vetal-esher/MT32-DIT/images/dit.png

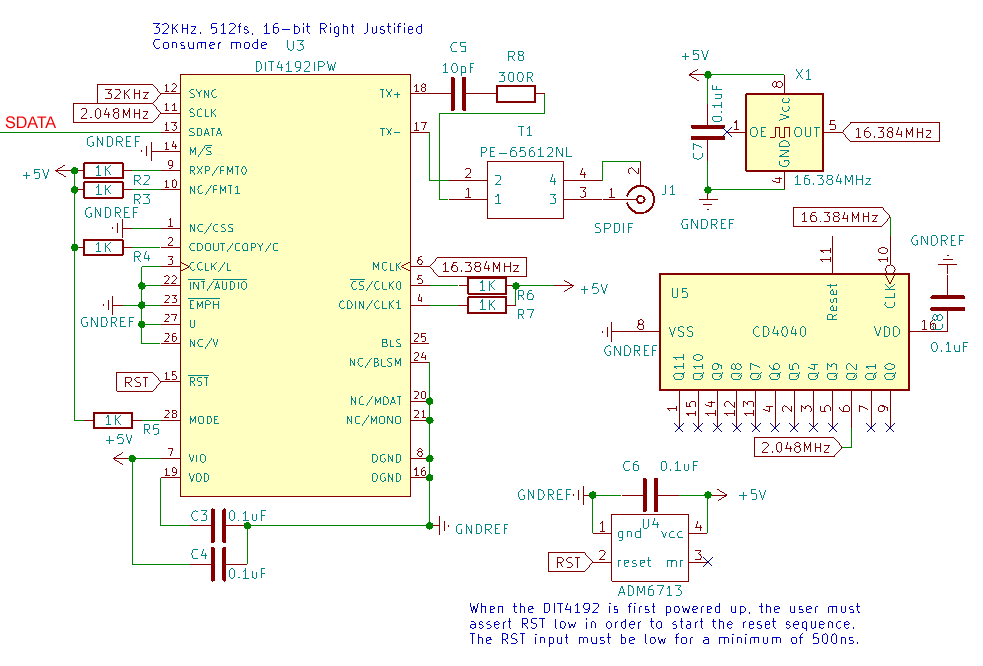
images/dit.png
