vetal-esher/MT32-DIT/images/oscil/A-B/pic_45_13.bmp

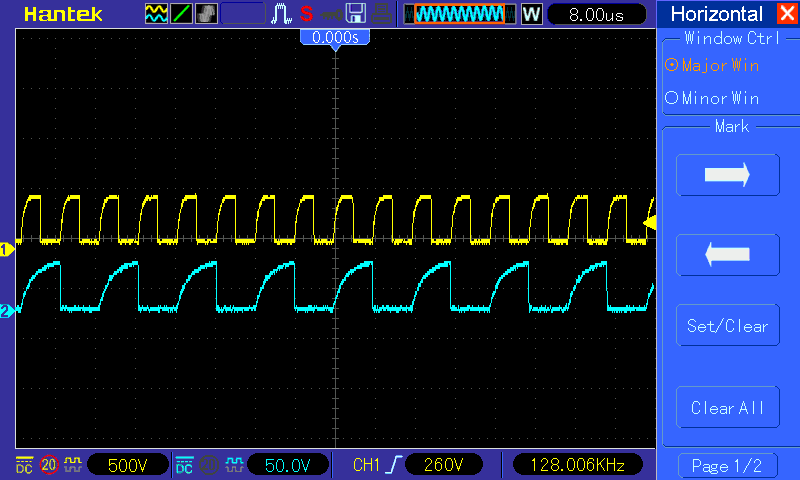
images/oscil/A-B/pic_45_13.bmp
