vetal-esher/MT32-DIT/images/oscil/A-C/pic_45_10.bmp

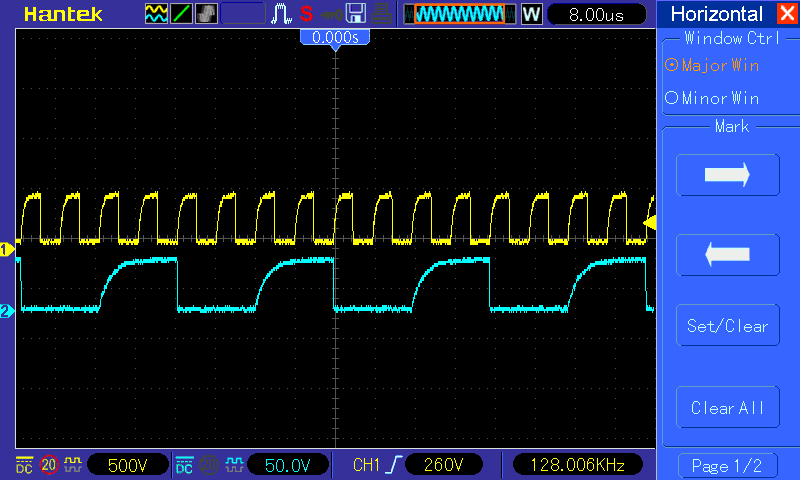
images/oscil/A-C/pic_45_10.bmp
