vetal-esher/MT32-DIT/images/oscil/A-C/pic_45_11.bmp

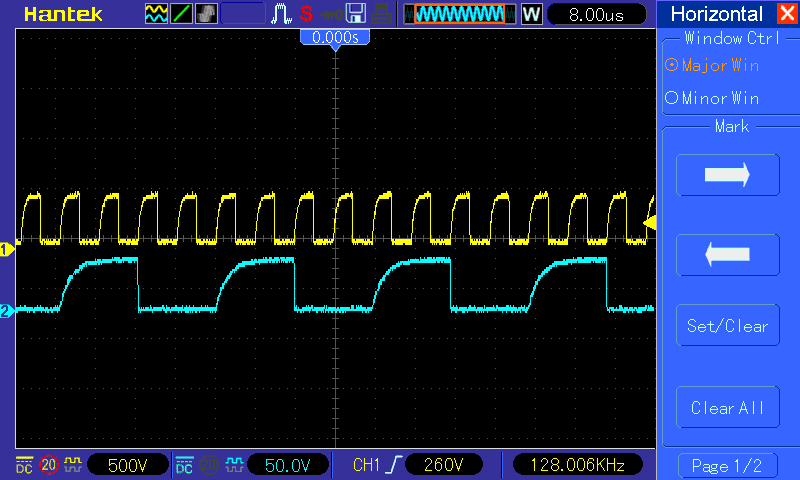
images/oscil/A-C/pic_45_11.bmp
