vetal-esher/MT32-DIT/images/oscil/A-C/pic_45_12.bmp

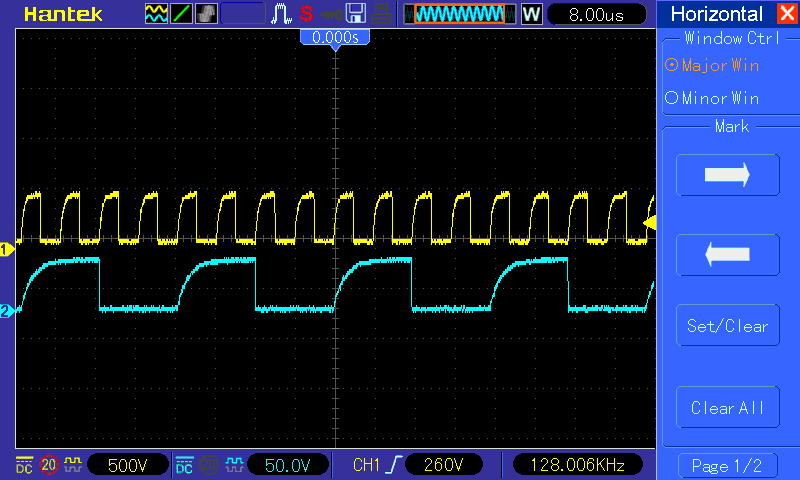
images/oscil/A-C/pic_45_12.bmp
