vetal-esher/MT32-DIT/images/oscil/A-INH/pic_45_17.bmp

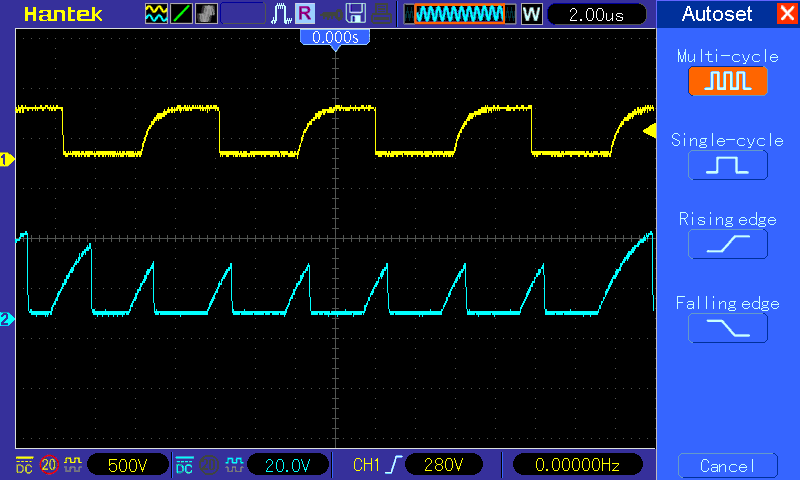
images/oscil/A-INH/pic_45_17.bmp
