vetal-esher/MT32-DIT/images/oscil/A-INH/pic_45_20.bmp

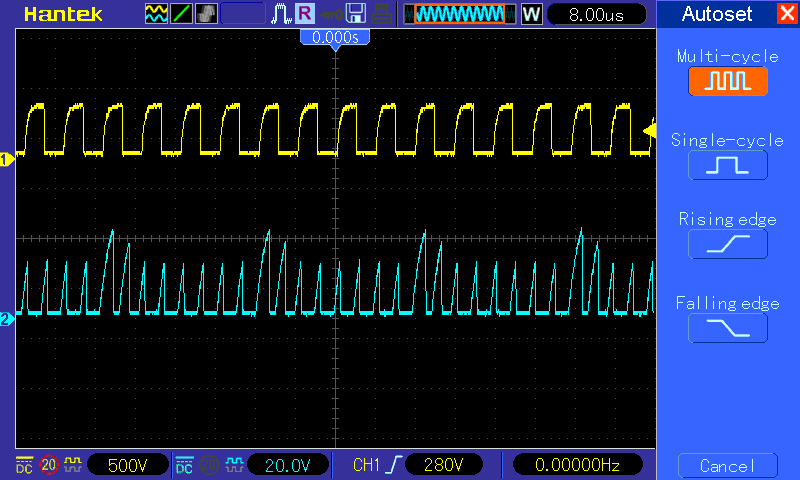
images/oscil/A-INH/pic_45_20.bmp
