vetal-esher/MT32-DIT/images/oscil/B-C/pic_45_15.bmp

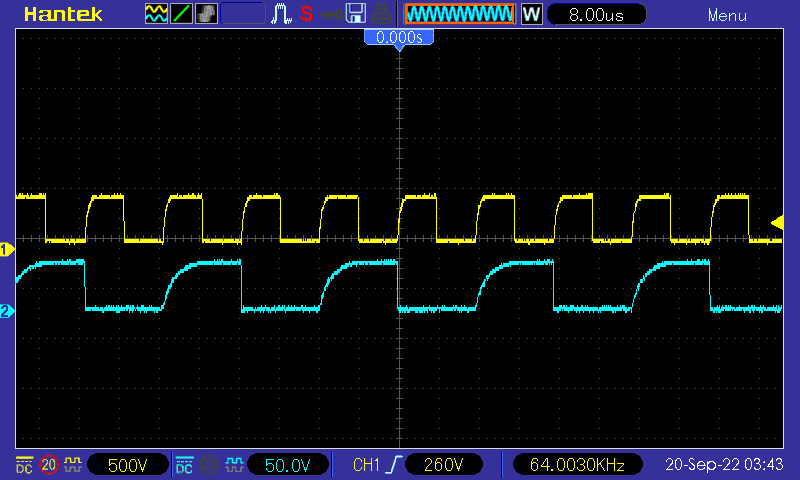
images/oscil/B-C/pic_45_15.bmp
