vetal-esher/MT32-DIT/images/oscil/B-C/pic_45_16.bmp

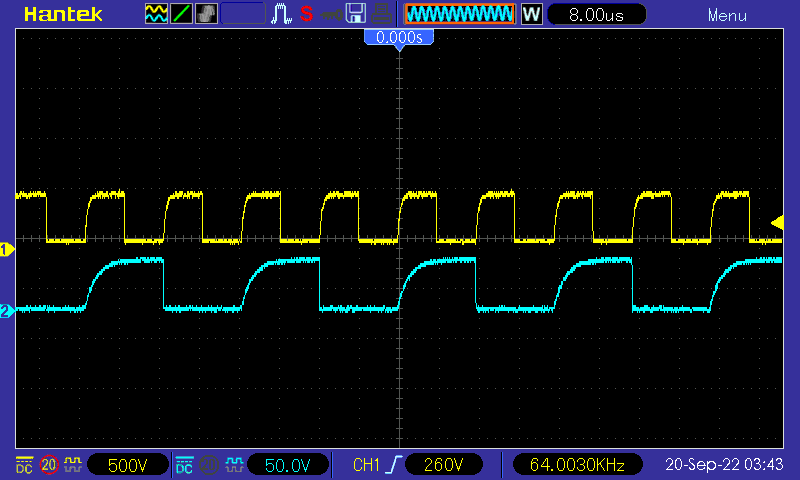
images/oscil/B-C/pic_45_16.bmp
