vetal-esher/MT32-DIT/images/pcm54str.png

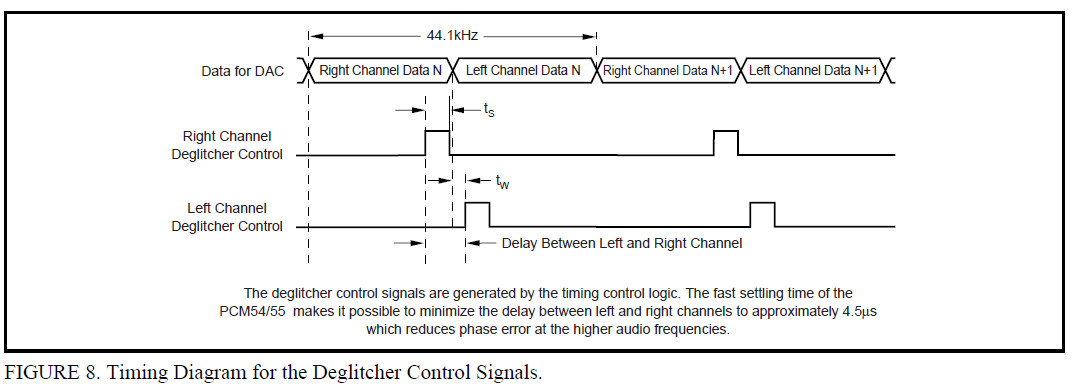
images/pcm54str.png
